motthomasn/QuadMAP-CMP_Sensor/Testing/Idle_Ch2Cyl1_Ch4Cyl2_Ch6ECUMAP.PNG

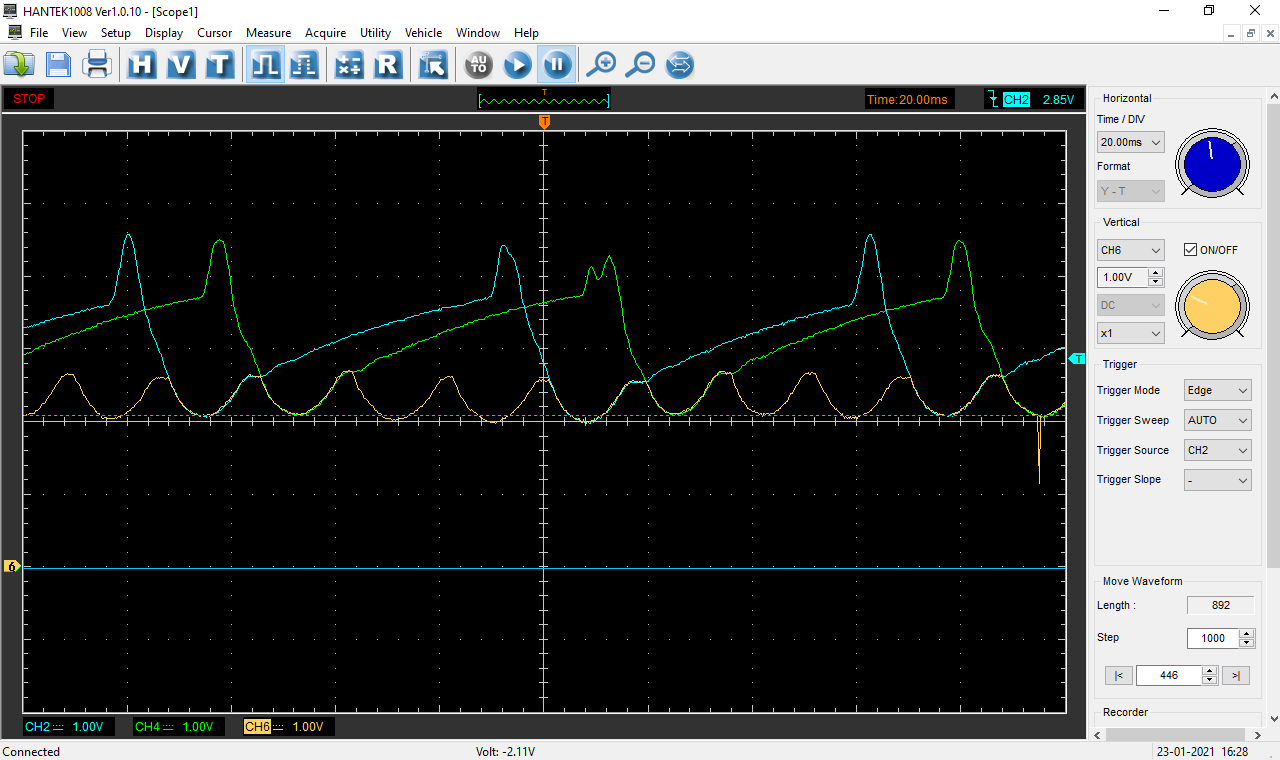
Testing/Idle_Ch2Cyl1_Ch4Cyl2_Ch6ECUMAP.PNG
